RBSC/HIC_Board/Pics/board_top.png

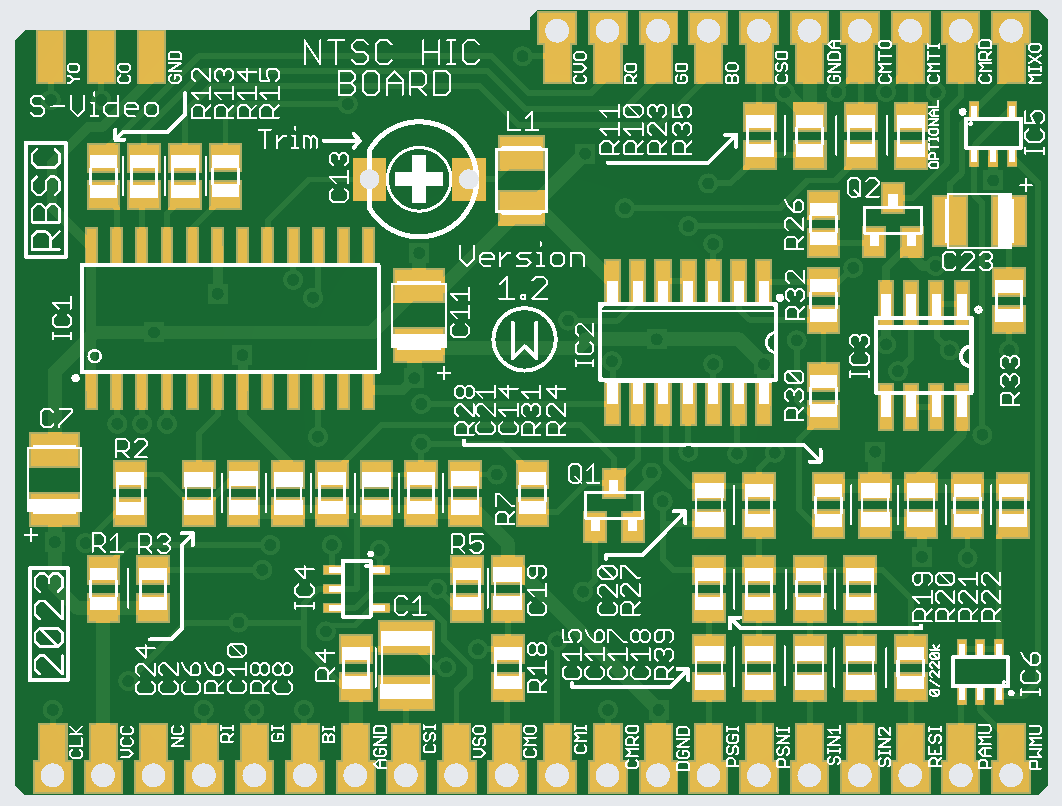
Pics/board_top.png
