RBSC/HIC_Board/Pics/svideo.jpg

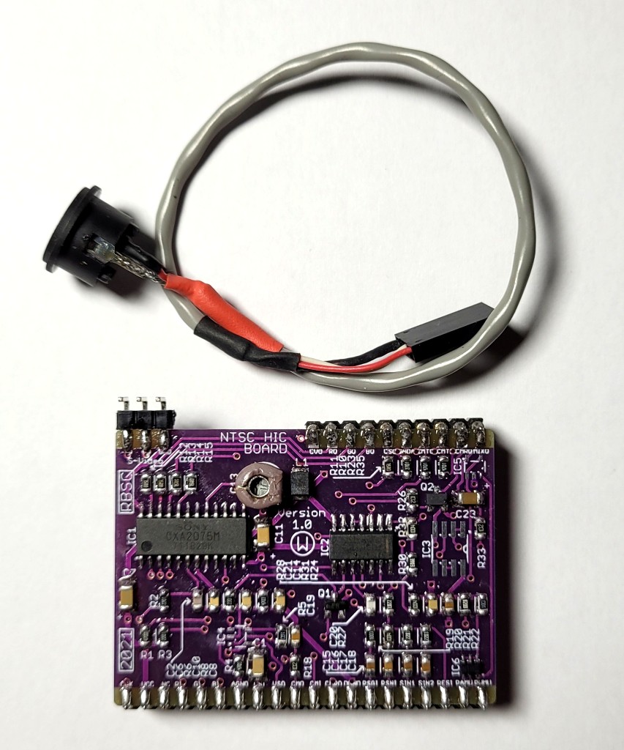
Pics/svideo.jpg
