RBSC/HIC_Board/Pics/74hc04_fix.jpg

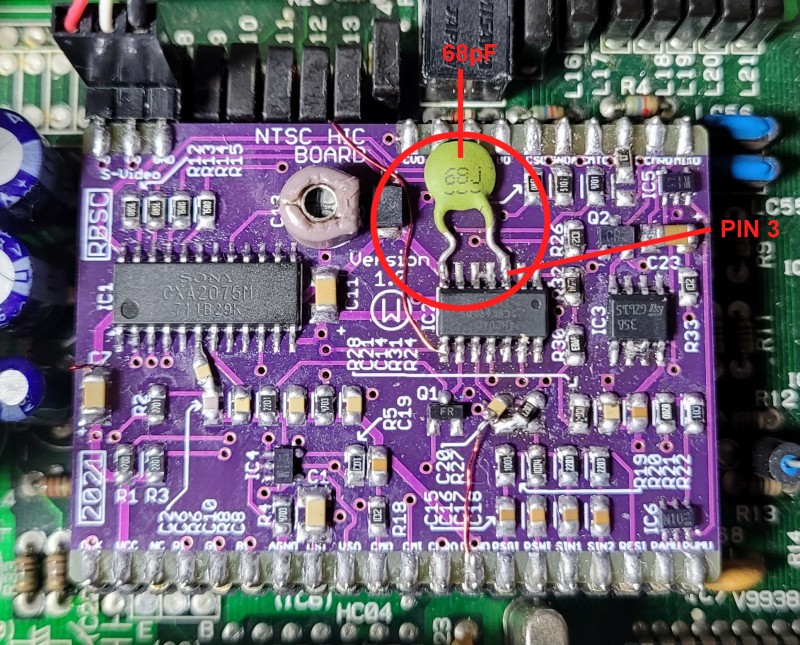
Pics/74hc04_fix.jpg
